az1zgq/PowerSupply/pcbDrawing/pdfDrawing/ИУ4.11.03.03.19.52.02.04.008 СП.pdf

Инв . № подл Подп . и Дата Взам .инв .№ Инв .№ дубл . Подп . и Дата Справ № Перв . примен . Изм . Лист № докум . Лит . Листов 1

МГТУ им . Н .Э .Баумана
Кафедра ИУ 4
Группа ИУ 4-52 Б

Лист

## Блок питания

перечень элементов

Подпись Дата

Разраб . Пров . Реценз . Н .контр . Утв . | Исмаилов А .К . Сергеева М .Д . Семенцов С .Г . | ИУ 4.11.03.03.19.05.02.04.0081 | 2
Копировал | Формат A4 Форм . | Зона Поз . | Обозначение | Наименование | Кол . Примечание
| | Детали
A3 | 16 ИУ 4.11.03.03.19.05.02.04.004 | Печатная плата

Документация

A3 | ИУ 4.11.03.03.19.05.02.04.005 СБ | Сборочный чертеж | 1
A3 | ИУ 4.11.03.03.19.05.02.04.001 Э 1 | Схема электрическая
| | структурная
A3 A1 | ИУ 4.11.03.03.19.05.02.04.001 ИУ 4.11.03.03.19.05.02.04.003 Э 3 | Чертеж печатной платы Схема электрическая | 1 1
| | принципиальная
A4 | ИУ 4.11.03.03.19.05.02.04.003 ПЭ 3 | Перечень элементов
A1 | ИУ 4.11.03.03.19.05.02.04.006 Э 1 | Измерительный стенд | 11
| | Схема электрическая
| | структурная | 1
| ИУ 4.11.03.03.19.05.02.04.007 ПД 1 | Плакат демонстрационный | 1
A3 | | | 1

Прочие изделия

| Диоды
| DB106, Диодный мост 1A 800 В | VD1
11 | 1N4148, Диод 150 мА 100 В | 111 VD3 VD2
| 1N5819, Диод Шоттки 1 А 40 В
10 6 | | C4 3
| Конденсаторы
| ECAP К 50-35 - 2.2 мкФ ,400 В | C1
21 | ECAP К 50-35 - 220 мкФ ,10 В ECAP К 50-35 - 10 мкФ ,400 В К 10-17 Б - 56 пФ ,50B | 1111 C2
20 | | C3

13

ВЫПОЛНЕНО В СТУДЕНЧЕСКОЙ ВЕРСИИ ПРОГРАММЫ AUTODESK ВЫПОЛНЕНО В СТУДЕНЧЕСКОЙ ВЕРСИИ ПРОГРАММЫ AUTODESK

Инв . № подл Подп . и Дата Взам .инв .№ Инв .№ дубл . Подп . и Дата Справ № Перв . примен . Изм . Лист № докум . Лит . Листов

### 1 МГТУ им . Н .Э .Баумана Кафедра ИУ

### 4 Группа ИУ 4-52

Б Лист Блок питания перечень элементов Подпись Дата Разраб . Пров . Реценз . Н .контр . Утв . | Исмаилов А .К . Сергеева М .Д . Семенцов С .Г . | ИУ 4.11.03.03.19.05.02.04.008

1

2 Копировал | Формат A4

### Форм . Зона

# Поз .Обозначение Наименование

Кол . Примечание Детали ИУ 4.11.03.03.19.05.02.04.004 Печатная плата Документация A3 ИУ 4.11.03.03.19.05.02.04.005 СБ Сборочный чертеж

ИУ 4.11.03.03.19.05.02.04.001 | 1 A3

Э

ИУ 4.11.03.03.19.05.02.04.003 1 | Схема электрическая структурная A1 | 1

Э

ИУ 4.11.03.03.19.05.02.04.003 ПЭ 3 | Схема электрическая принципиальная A4
ИУ 4.11.03.03.19.05.02.04.006 ИУ 4.11.03.03.19.05.02.04.001 3 | Перечень элементов A3 Чертеж печатной платы | 1 A1 1

Э

1 | Измерительный стенд
| В 1N4148, Диод 150 мА 100 | 1
31110 | В DB106, Диодный мост 1A 800 В | 1
| 1 А 40 | 1 VD3 VD1 VD2 Конденсаторы ECAP
К 50-35 - 2.2 мкФ ,400 В ECAP | 1
К 50-35 - 10 мкФ ,400 В | 1 C1C2C3C4 1
К 10-17 Б - 56 пФ ,50B ECAP | 1

## К 50-35 - 220 мкФ ,10 В

6212013 | структурная
| | 1 Схема электрическая ИУ 4.11.03.03.19.05.02.04.007 ПД
1 | Плакат демонстрационный
| 1N5819, Диод Шоттки | 1 Прочие изделия Диоды 16 1 A3 A3
| | 1

ВЫПОЛНЕНО В СТУДЕНЧЕСКОЙ ВЕРСИИ ПРОГРАММЫ AUTODESK ВЫПОЛНЕНО В СТУДЕНЧЕСКОЙ ВЕРСИИ ПРОГРАММЫ AUTODESK

ВЫПОЛНЕНО В СТУДЕНЧЕСКОЙ ВЕРСИИ ПРОГРАММЫ AUTODESK ВЫПОЛНЕНО В СТУДЕНЧЕСКОЙ ВЕРСИИ ПРОГРАММЫ AUTODESK
