az1zgq/PowerSupply/pcbDrawing/Experiment/2019-12-07_23-42-15.png

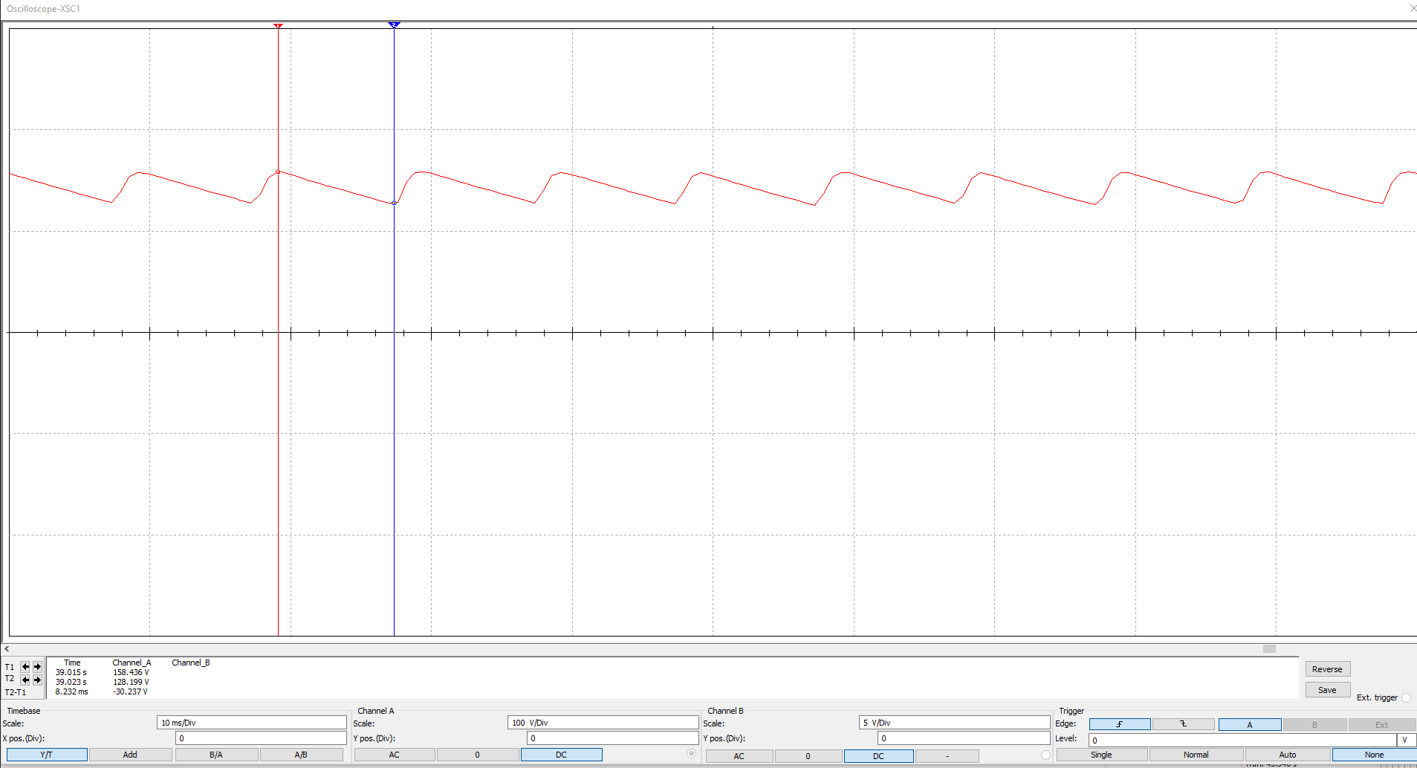
pcbDrawing/Experiment/2019-12-07_23-42-15.png
