az1zgq/PowerSupply/pcbDrawing/Experiment/2019-12-07_23-43-49.png

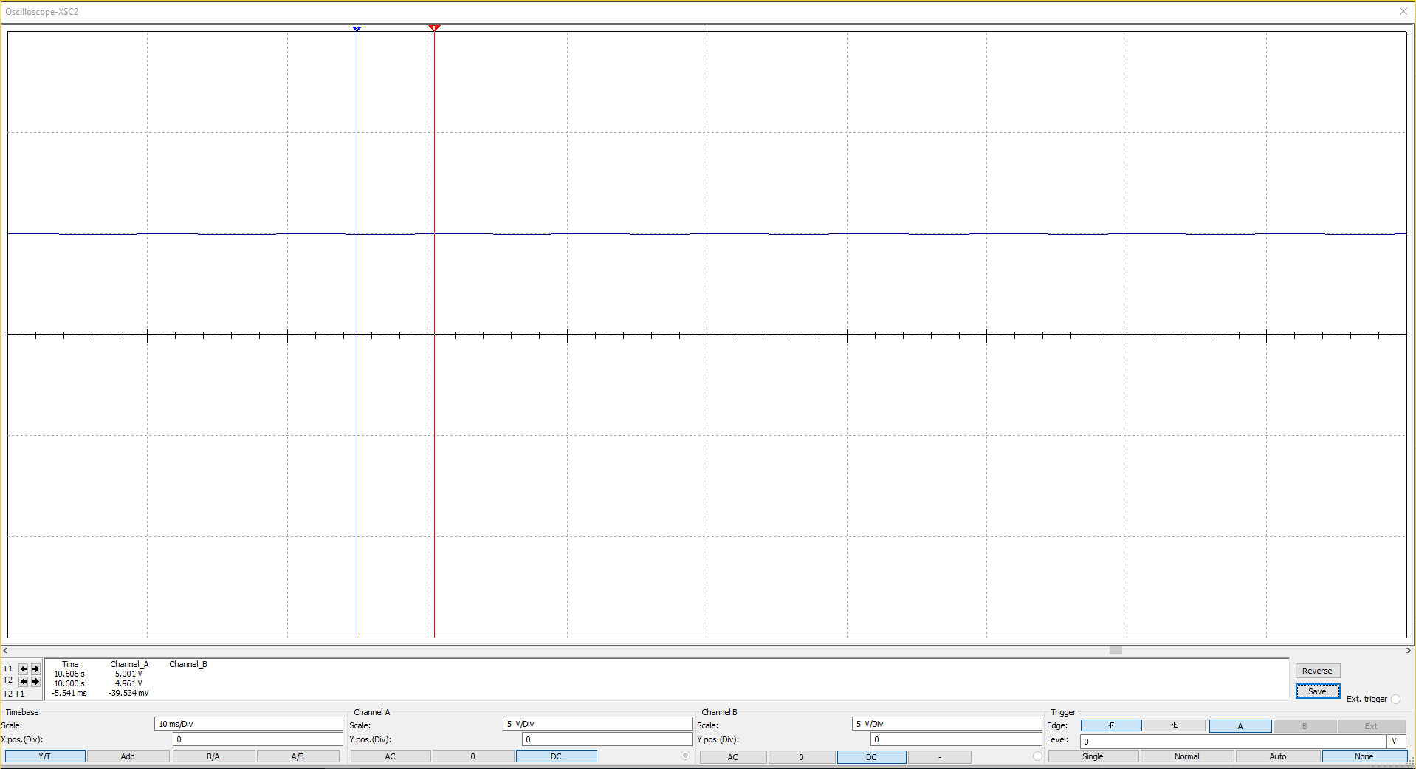
pcbDrawing/Experiment/2019-12-07_23-43-49.png
